BoujeeEnjinia1701/slopewatch/cad/drawings/SLW-DWG-001.pdf

CONCEPT, NOT FOR FABRICATION | SlopeWatch · github.com/BoujeeEnjinia1701/slopewatch

FRONT VIEW
Scale 1:50; looking at the front (along +Y)

TOP VIEW
Scale 1:50; looking down (along -Z)

RIGHT VIEW
Scale 1:50; looking at the right side (along -X)

4628

435 4660

GROUND

3,510 top of beacon

3,200 mast

1,750 node

600

800 embed

400 capsule

1,300 | 1,600

1-3 TILT STAKE (DETAIL A)

4 CRACK GAUGE

6 FIELDNODE CORE

7 ALERT UNIT, SIDE MOUNTED

7 KEYED SWITCH POST

8 MAST (SITE OPTION)

+X DOWNSLOPE ON SITE; NODE AND HORN FACE -Y

DETAIL A
Stake section, scale 1:10

2 CAPSULE 34 x 130

FOAM PLUG

STAND TUBE 40

GROUT 110 x 450

1 PIPE 48.3 x 3.2

3 HEAD 110, CONDUIT IN AND OUT

330

GROUND

MAIN DIMENSIONS AND INTERFACES (MM)
Stake 48.3 x 3.2 galv. pipe, 1000 long, 800 in ground, screwed end cap Hole 110 dia x 829; grout 3.7 L; capsule 400 deep on stand tube Crack gauge: anchors 900 apart, pins 20 x 700, stroke 100
Mast (option) 48.3 x 3.2, 3,200 high; footing 320 x 600
Switch post 26.9 dia, 1,400 high, 5 m from mast on site
FieldNode massing per FND-DDR-003; node bottom 1,750; alert unit on V-blocks and bands Bus 4-core 0.5 mm2 on the 5 V port; stakes 10 m apart, cable 59 m on site
REV | DESCRIPTION | DATE | BY
P1 | Preliminary GA for TRL 3 (from cad/src/model.py) | 2026-09-25 | AC
P2 | Keyed switch on own post 5 m from mast; mast a site option (DDR-002) | 2026-09-25 | AC
P3 | Layout and labels tidied | 2026-09-25 | AC
P4 | Constructable design (DDR-003) | 2026-10-01 | AC
P5 | SLW-DEC-001: stake head marking, back plate wall holes | 2026-10-02 | AC
SLOPEWATCH | github.com/BoujeeEnjinia1701/slopewatch

## General arrangement

DRAWING NO.
SLW-DWG-001

REV
P5

SHEET
1 of 1

SIZE

## ANSI B

SCALE
1:50

UNITS
mm
PROJECTION | DATE
2026-10-02

DRAWN
Amish Chadha

MATERIAL / NOTES
Galvanized steel, cement grout, bought-in parts per bom/bom.csv. PRELIMINARY, NOT FOR FABRICATION
Licensed CERN-OHL-S-2.0 · Design Molecule Lab · designmolecule.com | Generated from cad/src; do not edit by hand
