BoujeeEnjinia1701/slopewatch/cad/drawings/SLW-DWG-101.pdf

BUILD PLAN SKETCH, PLAN NOT YET BUILT SlopeWatch · github.com/BoujeeEnjinia1701/slopewatch

FRONT VIEW
Scale 1:10; looking at the front (along +Y)

TOP VIEW
Scale 1:10; looking down (along -Z)

RIGHT VIEW
Scale 1:10; looking at the right side (along -X)

60

60 1009

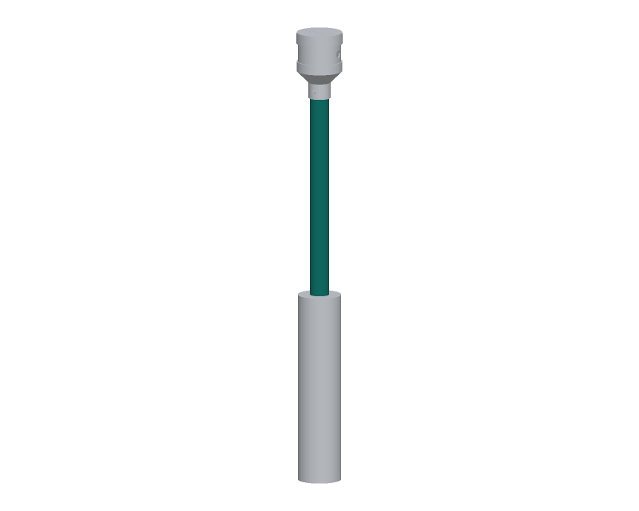
[picture p7: figure]

WHERE IT GOES
This part in colour, its neighbours in grey

HOW TO MAKE IT AND HOW IT FITS
Make three. Cut 1,000 mm of 48.3 x 3.2 mm galvanized pipe with one end threaded 1.5 in (have the merchant cut and thread it). Screw the 1.5 in malleable-iron end cap onto the threaded end with thread sealant, hand tight plus a quarter turn with a pipe wrench. File the other (top) end square and deburr inside and out.
Paint a ground mark round the pipe 200 mm below the top; the pipe goes into the ground up to this mark (800 mm buried).
Touch up cut galvanizing with zinc-rich paint.
Do not drill the head screw holes yet: they are drilled through
the head's socket at assembly so they line up (step 6).
Fit: the cap keeps grout and water out of the bottom; the stand tube stands on the cap's floor inside the pipe.
Check: blow down the pipe; no light or air through the cap.
REV | DESCRIPTION | DATE | BY
P1 | Making sketch for the prototype build plan | 2026-10-01 | AC
SLOPEWATCH | github.com/BoujeeEnjinia1701/slopewatch

## SlopeWatch stake pipe with end cap (make 3): making sketch

DRAWING NO.
SLW-DWG-101

REV
P1

SHEET
1 of 1

SIZE

## ANSI B

SCALE
1:10

UNITS
mm
PROJECTION | DATE
2026-10-01

DRAWN
Amish Chadha

MATERIAL / NOTES
Galvanized steel pipe 48.3 x 3.2 mm (1.5 in), threaded one end; malleable-iron cap
Licensed CERN-OHL-S-2.0 · Design Molecule Lab · designmolecule.com | Generated from cad/src; do not edit by hand
