BoujeeEnjinia1701/slopewatch/cad/drawings/SLW-DWG-102.pdf

BUILD PLAN SKETCH, PLAN NOT YET BUILT SlopeWatch · github.com/BoujeeEnjinia1701/slopewatch

FRONT VIEW
Scale 1:5; looking at the front (along +Y)

TOP VIEW
Scale 1:5; looking down (along -Z)

RIGHT VIEW
Scale 1:5; looking at the right side (along -X)

40

40 335

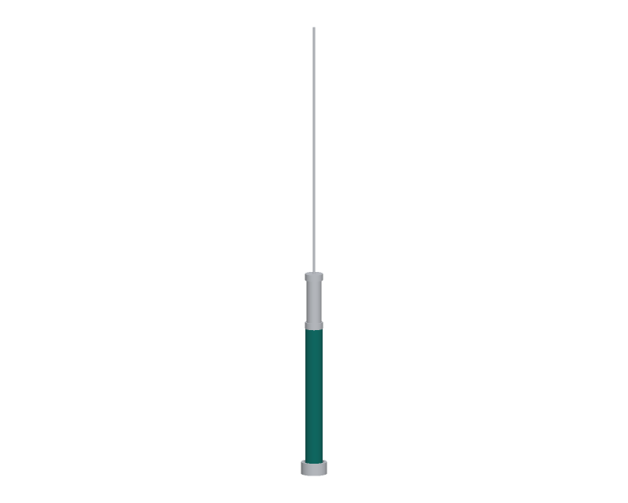
[picture p8: figure]

WHERE IT GOES
This part in colour, its neighbours in grey

HOW TO MAKE IT AND HOW IT FITS
Make three. Cut 335 mm of 40 mm OD PVC pipe, ends square. Deburr both ends; chamfer the outside edges 1 mm so it slides down the 41.9 mm bore of the stake pipe without catching. Its length sets the capsule depth: capsule centre 400 mm below ground when the stand tube sits on the end cap floor. Fit: drops down the pipe and stands on the cap floor, 0.95 mm clear of the bore all round. The capsule's lower collar sits on its top rim; the capsule itself is 1 mm inside the rim.
Mark the length on the tube; check it with a tape before cutting, since a 10 mm error moves the capsule 10 mm.
Check: 335 mm long, within 2 mm; slides freely down an offcut of the stake pipe.
REV | DESCRIPTION | DATE | BY
P1 | Making sketch for the prototype build plan | 2026-10-01 | AC
SLOPEWATCH | github.com/BoujeeEnjinia1701/slopewatch

## SlopeWatch stand tube (make 3): making sketch

DRAWING NO.
SLW-DWG-102

REV
P1

SHEET
1 of 1

SIZE

## ANSI B

SCALE
1:5

UNITS
mm
PROJECTION | DATE
2026-10-01

DRAWN
Amish Chadha

MATERIAL / NOTES
PVC pressure pipe 40 mm OD, 2 mm wall
Licensed CERN-OHL-S-2.0 · Design Molecule Lab · designmolecule.com | Generated from cad/src; do not edit by hand
