BoujeeEnjinia1701/slopewatch/cad/drawings/SLW-DWG-103.pdf

BUILD PLAN SKETCH, PLAN NOT YET BUILT SlopeWatch · github.com/BoujeeEnjinia1701/slopewatch

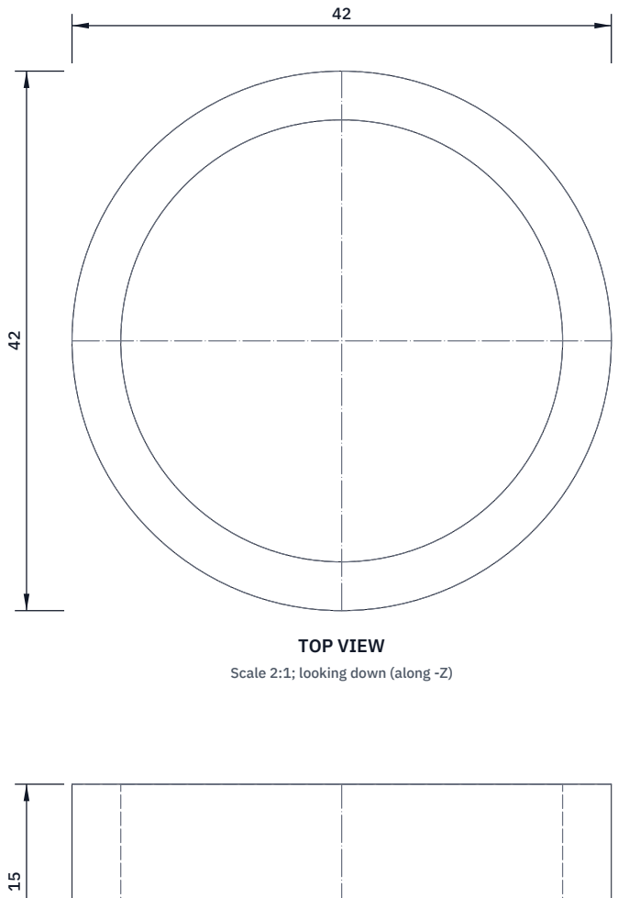
[picture p9: figure]
TOP VIEW; Scale 2:1; looking down (along -Z)

FRONT VIEW
Scale 2:1; looking at the front (along +Y)

RIGHT VIEW
Scale 2:1; looking at the right side (along -X)

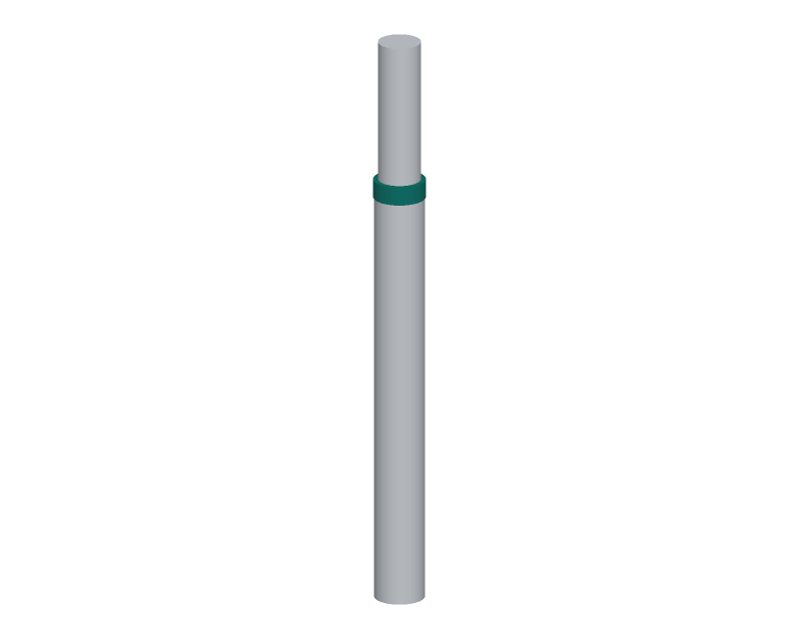
[picture p10: figure]

WHERE IT GOES
This part in colour, its neighbours in grey

HOW TO MAKE IT AND HOW IT FITS
Make six, two per capsule. Print ASA flat, 100 % infill. Ring 41.5 mm outside, 34 mm inside, 15 mm long.
Print one first and check it: it must be a light press fit on
the capsule tube and slide freely in an offcut of the stake
pipe (bore 41.9 mm). Adjust the outside size in steps of 0.2 mm. Fit: one collar flush with each end of the capsule, with a drop
of polyurethane adhesive. They hold the capsule on the pipe axis so it tilts with the pipe; 0.2 mm clearance to the bore.
The lower collar rests on the stand tube's top rim.
Check: on the capsule, both collars turn freely in the pipe offcut and the capsule does not rock when held level.
REV | DESCRIPTION | DATE | BY
P1 | Making sketch for the prototype build plan | 2026-10-01 | AC
SLOPEWATCH | github.com/BoujeeEnjinia1701/slopewatch

## SlopeWatch capsule centring collar (make 6): making sketch

DRAWING NO.
SLW-DWG-103

REV
P1

SHEET
1 of 1

SIZE

## ANSI B

SCALE
2:1

UNITS
mm
PROJECTION | DATE
2026-10-01

DRAWN
Amish Chadha

MATERIAL / NOTES
ASA, 3D printed, 100 % infill
Licensed CERN-OHL-S-2.0 · Design Molecule Lab · designmolecule.com | Generated from cad/src; do not edit by hand
