BoujeeEnjinia1701/slopewatch/cad/drawings/SLW-DWG-104.pdf

BUILD PLAN SKETCH, PLAN NOT YET BUILT SlopeWatch · github.com/BoujeeEnjinia1701/slopewatch

FRONT VIEW
Scale 1:2; looking at the front (along +Y)

TOP VIEW
Scale 1:2; looking down (along -Z)

RIGHT VIEW
Scale 1:2; looking at the right side (along -X)

42

42 130

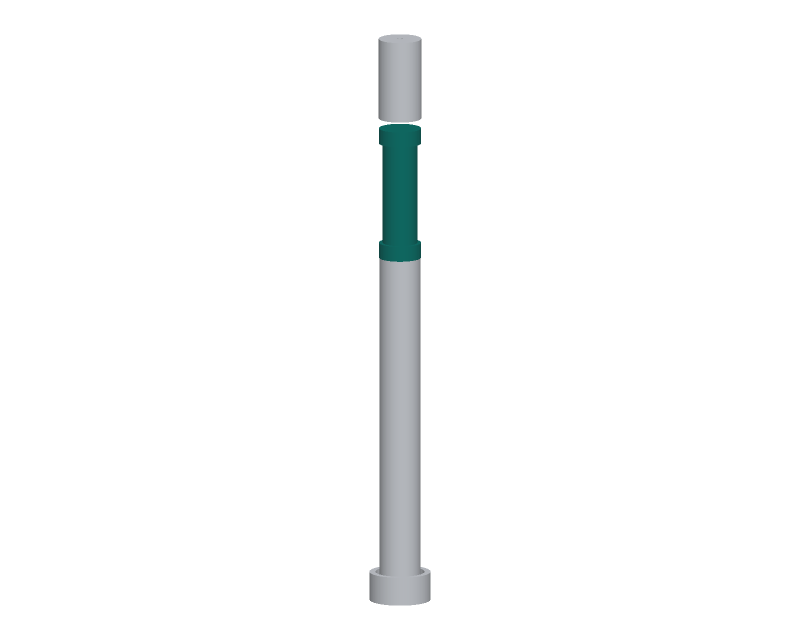
[picture p11: figure]

WHERE IT GOES
This part in colour, its neighbours in grey

HOW TO MAKE IT AND HOW IT FITS
Make three. Tube 34 mm OD x 130 mm, polycarbonate, 2 mm wall. Board: inclinometer, microcontroller, RS-485 transceiver and 3.3 V regulator, at most 28 mm wide, flashed and bench-read first.
Mark the board's X axis with an arrow on the tube label: the arrow points downslope when the capsule is lowered (step 4).
Lead: 0.8 m of 4-core 0.25 mm2 shielded cable, out of the top centre. Seal the bottom with a glued disc, slide the board in on a
printed carrier square to the tube, and pot it full with
polyurethane potting compound; cure as its maker says.
Glue a centring collar flush on each end (SLW-DWG-103). Fit: rests on the stand tube on its lower collar, centred in the pipe by both collars; the foam plug sits 10 mm above it. Check: reads within 0.1 degree of a spirit level on the bench.
REV | DESCRIPTION | DATE | BY
P1 | Making sketch for the prototype build plan | 2026-10-01 | AC
SLOPEWATCH | github.com/BoujeeEnjinia1701/slopewatch

## SlopeWatch sensor capsule (make 3): making sketch

DRAWING NO.
SLW-DWG-104

REV
P1

SHEET
1 of 1

SIZE

## ANSI B

SCALE
1:2

UNITS
mm
PROJECTION | DATE
2026-10-01

DRAWN
Amish Chadha

MATERIAL / NOTES
Polycarbonate tube 34 x 2 mm, potted electronics
Licensed CERN-OHL-S-2.0 · Design Molecule Lab · designmolecule.com | Generated from cad/src; do not edit by hand
