BoujeeEnjinia1701/slopewatch/cad/drawings/SLW-DWG-105.pdf

BUILD PLAN SKETCH, PLAN NOT YET BUILT SlopeWatch · github.com/BoujeeEnjinia1701/slopewatch

FRONT VIEW
Scale 1:5; looking at the front (along +Y)

TOP VIEW
Scale 1:5; looking down (along -Z)

RIGHT VIEW
Scale 1:5; looking at the right side (along -X)

176

117 170

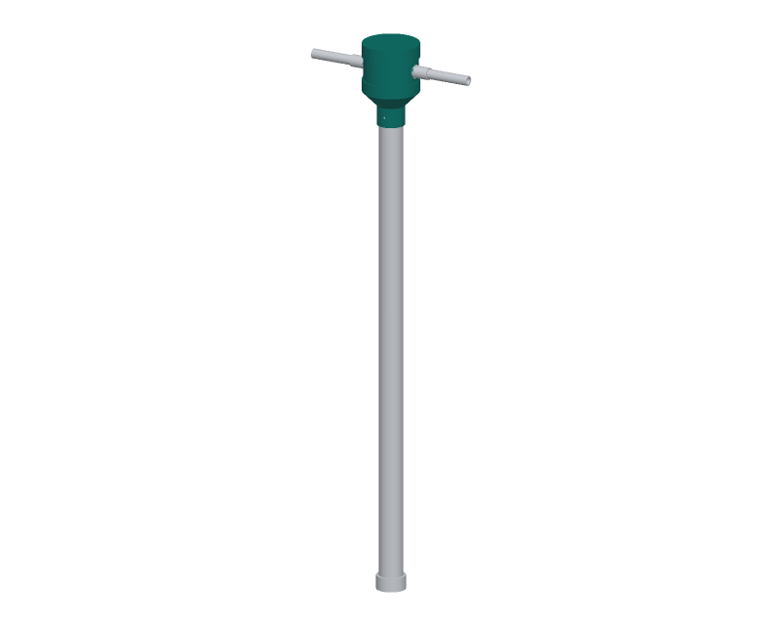
[picture p12: figure]

WHERE IT GOES
This part in colour, its neighbours in grey

HOW TO MAKE IT AND HOW IT FITS
Make three from stock 110 mm PVC drainage parts: a 110 x 50 mm concentric reducer, a 110 mm end cap and 94 mm of 110 mm pipe. Cut the 110 pipe square to 94 mm and deburr.
Drill two 20.5 mm holes for the M20 conduit fittings, opposite each other, centred 46 mm up from the pipe's lower end (check the fitting's datasheet). One faces upslope, one downslope.
Push the pipe fully into the reducer's 110 socket and the cap onto its top; solvent-cement both joints.
Paint the outside signal amber. Round the cap skirt wind 25 mm retroreflective tape; stick a 40 x 30 mm ID label on the -Y side and an arrow on the crown pointing downslope (+X).
Fit: the reducer's 50 mm socket goes over the stake pipe on a tape wrap; two M5 self-tapping screws hold it, drilled through the socket into the pipe at assembly, 20 mm above the socket rim. Check: the head stands 330 mm above ground on the stake.
REV | DESCRIPTION | DATE | BY
P1 | Making sketch for the prototype build plan | 2026-10-01 | AC
P2 | SLW-DEC-001: head marking, wall holes, 60.3 mm site mast | 2026-10-02 | AC
SLOPEWATCH | github.com/BoujeeEnjinia1701/slopewatch

## SlopeWatch stake head (make 3): making sketch

DRAWING NO.
SLW-DWG-105

REV
P2

SHEET
1 of 1

SIZE

## ANSI B

SCALE
1:5

UNITS
mm
PROJECTION | DATE
2026-10-02

DRAWN
Amish Chadha

MATERIAL / NOTES
Stock PVC drainage fittings, 110 mm
Licensed CERN-OHL-S-2.0 · Design Molecule Lab · designmolecule.com | Generated from cad/src; do not edit by hand
