BoujeeEnjinia1701/slopewatch/cad/drawings/SLW-DWG-106.pdf

BUILD PLAN SKETCH, PLAN NOT YET BUILT SlopeWatch · github.com/BoujeeEnjinia1701/slopewatch

FRONT VIEW
Scale 1:10; looking at the front (along +Y)

TOP VIEW
Scale 1:10; looking down (along -Z)

RIGHT VIEW
Scale 1:10; looking at the right side (along -X)

20

20 700

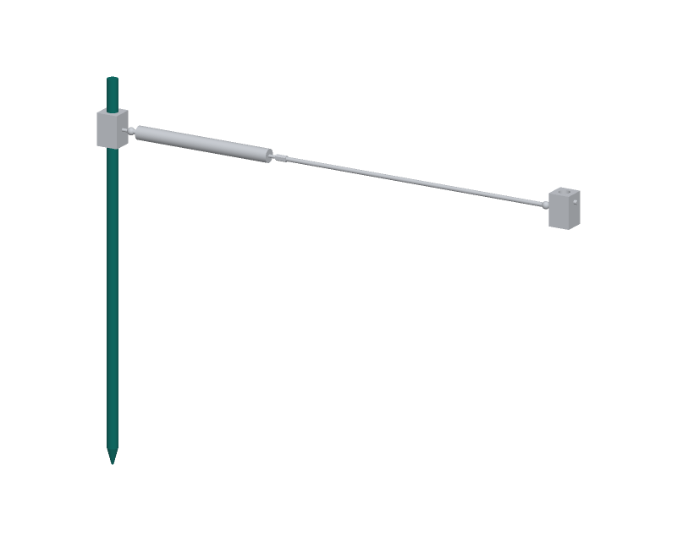
[picture p13: figure]

WHERE IT GOES
This part in colour, its neighbours in grey

HOW TO MAKE IT AND HOW IT FITS
Make two. Cut 700 mm of 20 mm round bar.
Grind a point 30 mm long on one end, about 4 mm across the tip. Chamfer the top edge 2 mm so a sledge does not mushroom it. Paint a ring 500 mm from the tip: drive to this ring, which leaves 200 mm above ground.
Paint the exposed part (or use galvanized bar).
Fit: driven upright 900 mm apart, one each side of the crack, on a line square to it. Each carries a clamp block with its centre 110 mm above ground.
Check: a level on the pin shows it upright within 2 degrees.
REV | DESCRIPTION | DATE | BY
P1 | Making sketch for the prototype build plan | 2026-10-01 | AC
SLOPEWATCH | github.com/BoujeeEnjinia1701/slopewatch

## SlopeWatch anchor pin (make 2): making sketch

DRAWING NO.
SLW-DWG-106

REV
P1

SHEET
1 of 1

SIZE

## ANSI B

SCALE
1:10

UNITS
mm
PROJECTION | DATE
2026-10-01

DRAWN
Amish Chadha

MATERIAL / NOTES
Mild steel round bar 20 mm, galvanized or painted
Licensed CERN-OHL-S-2.0 · Design Molecule Lab · designmolecule.com | Generated from cad/src; do not edit by hand
