BoujeeEnjinia1701/slopewatch/cad/drawings/SLW-DWG-107.pdf

BUILD PLAN SKETCH, PLAN NOT YET BUILT SlopeWatch · github.com/BoujeeEnjinia1701/slopewatch

FRONT VIEW
Scale 1:1; looking at the front (along +Y)

TOP VIEW
Scale 1:1; looking down (along -Z)

RIGHT VIEW
Scale 1:1; looking at the right side (along -X)

40

40 60

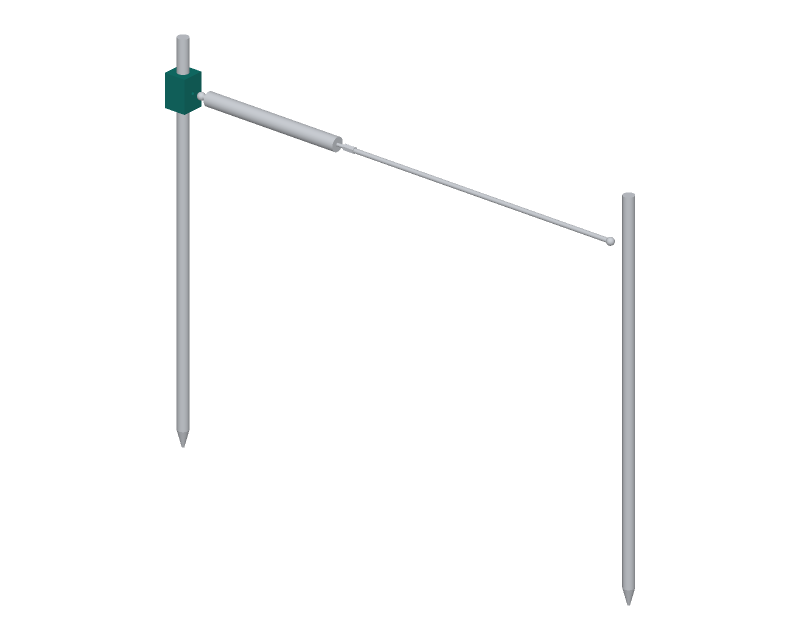
[picture p14: figure]

WHERE IT GOES
This part in colour, its neighbours in grey

HOW TO MAKE IT AND HOW IT FITS
Make two the same. Saw 60 mm off 40 x 40 mm bar; file square. Bore: drill 20.5 mm right through the 40 x 40 faces, on centre. Stud hole: on one 40 x 60 side face, at mid-height (30 mm up) and centred, drill 5.0 mm 12 deep and tap M6 10 deep.
Set screw hole: on the opposite side face, 45 mm up and centred, drill 6.8 mm through into the bore and tap M8.
Fit: slides onto the pin; the stud face points at the other pin across the crack. Set the block centre 110 mm above ground and tighten the M8 set screw onto the pin.
Screw the M6 stud of a rod-end ball joint 10 mm into the stud hole with medium threadlocker.
Check: the block slides on a 20 mm bar with no shake beyond 0.5 mm.
REV | DESCRIPTION | DATE | BY
P1 | Making sketch for the prototype build plan | 2026-10-01 | AC
SLOPEWATCH | github.com/BoujeeEnjinia1701/slopewatch

## SlopeWatch crack gauge clamp block (make 2): making sketch

DRAWING NO.
SLW-DWG-107

REV
P1

SHEET
1 of 1

SIZE

## ANSI B

SCALE
1:1

UNITS
mm
PROJECTION | DATE
2026-10-01

DRAWN
Amish Chadha

MATERIAL / NOTES
Aluminium square bar 40 x 40 mm, 6082
Licensed CERN-OHL-S-2.0 · Design Molecule Lab · designmolecule.com | Generated from cad/src; do not edit by hand
