BoujeeEnjinia1701/slopewatch/cad/drawings/SLW-DWG-108.pdf

BUILD PLAN SKETCH, PLAN NOT YET BUILT SlopeWatch · github.com/BoujeeEnjinia1701/slopewatch

FRONT VIEW
Scale 1:5; looking at the front (along +Y)

TOP VIEW
Scale 1:5; looking down (along -Z)

RIGHT VIEW
Scale 1:5; looking at the right side (along -X)

8

8 501

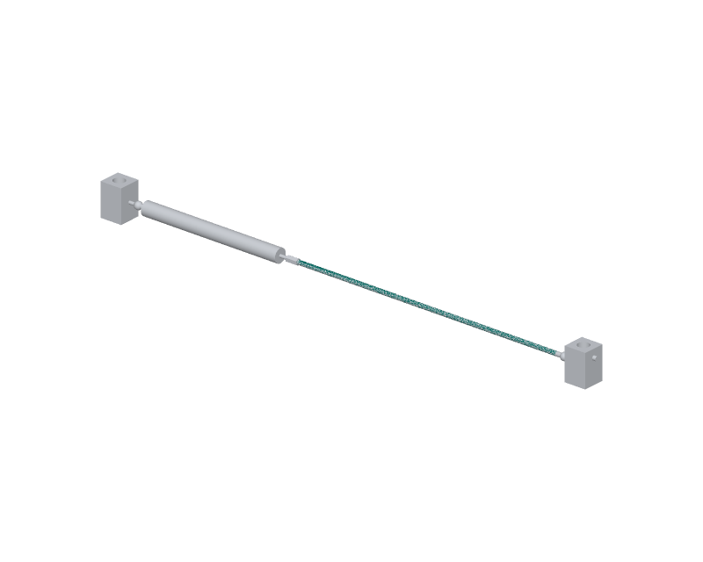
[picture p15: figure]

WHERE IT GOES
This part in colour, its neighbours in grey

HOW TO MAKE IT AND HOW IT FITS
Cut 501 mm of 8 mm stainless bar, ends square.
Centre-drill each end in a drill press with the bar held
upright in a V-block; drill 5.0 mm 15 deep and tap M6.
Screw an M6 x 20 stud into each end with medium threadlocker, 10 mm in and 10 mm out.
Fit: one end into the coupling nut on the sensor's plunger; the other into the downslope rod-end ball joint on its stud.
Set the plunger 15 mm out of the sensor body before tightening, so the gauge can read 85 mm of opening and 15 mm of closing. Check: 501 mm long within 1 mm; straight within 1 mm
when rolled on a flat bench.
REV | DESCRIPTION | DATE | BY
P1 | Making sketch for the prototype build plan | 2026-10-01 | AC
SLOPEWATCH | github.com/BoujeeEnjinia1701/slopewatch

## SlopeWatch crack gauge extension rod: making sketch

DRAWING NO.
SLW-DWG-108

REV
P1

SHEET
1 of 1

SIZE

## ANSI B

SCALE
1:5

UNITS
mm
PROJECTION | DATE
2026-10-01

DRAWN
Amish Chadha

MATERIAL / NOTES
Stainless steel round bar 8 mm, 304
Licensed CERN-OHL-S-2.0 · Design Molecule Lab · designmolecule.com | Generated from cad/src; do not edit by hand
