BoujeeEnjinia1701/slopewatch/cad/drawings/SLW-DWG-109.pdf

BUILD PLAN SKETCH, PLAN NOT YET BUILT SlopeWatch · github.com/BoujeeEnjinia1701/slopewatch

FRONT VIEW
Scale 1:10; looking at the front (along +Y)

TOP VIEW
Scale 1:10; looking down (along -Z)

RIGHT VIEW
Scale 1:10; looking at the right side (along -X)

1150

250 250

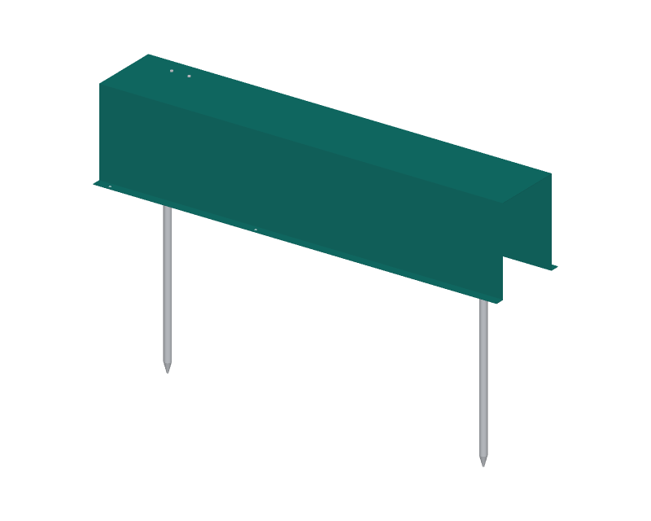
[picture p16: figure]

WHERE IT GOES
This part in colour, its neighbours in grey

HOW TO MAKE IT AND HOW IT FITS
Blank 1,150 x 750 mm of 1.5 mm galvanized sheet. Fold lines along the 1,150 mm length at 25, 275, 475 and 725 mm from one edge. Fold the two outer 25 mm strips out (feet) and the 250 mm legs down, to an inverted channel 200 wide, 250 high, with feet.
Have it folded by a sheet metal shop, or fold it between two
1.2 m steel angles clamped to a bench.
Peg holes: four 9 mm, centred in the feet, 40 and 455 mm from the upslope end. Only the upslope half is pegged, so the crack
can open under the downslope half.
Reader screw holes: two 4.5 mm in the web, 100 and 150 mm from the upslope end, 52 mm to one side of the centre line.
Fit: stands over the gauge on its feet, 48 mm above the pin tops. Check: the web is flat and the legs square within 3 mm.
REV | DESCRIPTION | DATE | BY
P1 | Making sketch for the prototype build plan | 2026-10-01 | AC
SLOPEWATCH | github.com/BoujeeEnjinia1701/slopewatch

## SlopeWatch crack gauge guard: making sketch

DRAWING NO.
SLW-DWG-109

REV
P1

SHEET
1 of 1

SIZE

## ANSI B

SCALE
1:10

UNITS
mm
PROJECTION | DATE
2026-10-01

DRAWN
Amish Chadha

MATERIAL / NOTES
Galvanized steel sheet 1.5 mm
Licensed CERN-OHL-S-2.0 · Design Molecule Lab · designmolecule.com | Generated from cad/src; do not edit by hand
