BoujeeEnjinia1701/slopewatch/cad/drawings/SLW-DWG-110.pdf

BUILD PLAN SKETCH, PLAN NOT YET BUILT SlopeWatch · github.com/BoujeeEnjinia1701/slopewatch

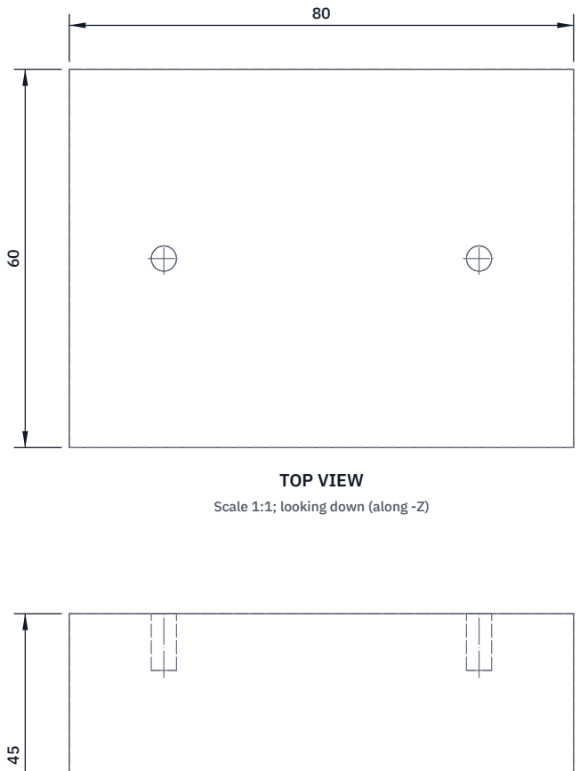
[picture p17: figure]
TOP VIEW; Scale 1:1; looking down (along -Z)

FRONT VIEW
Scale 1:1; looking at the front (along +Y)

RIGHT VIEW
Scale 1:1; looking at the right side (along -X)

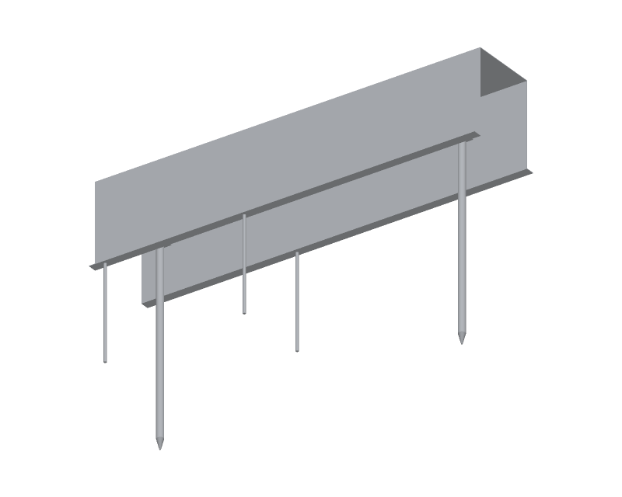
[picture p18: figure]

WHERE IT GOES
This part in colour, its neighbours in grey

HOW TO MAKE IT AND HOW IT FITS
A bought IP67 box, 80 x 60 x 45 mm, holding the reader board. Base (the face that goes against the guard web): two 4 mm holes 50 mm apart on the long centre line, matching the web holes. Seal under each screw head with a nylon washer.
Downslope end: one 20.5 mm hole, centred, for the M20 conduit fitting that carries the bus out.
Upslope end: one 12.5 mm hole for an M12 gland for the sensor lead. Fit the reader board on its standoffs; terminate the sensor lead
and the bus in lever connectors as the bus diagram shows.
Fit: hangs under the guard web at the upslope end, lid down,
12 mm clear of the upslope pin.
Check: lid gasket seated; the box hangs level.
REV | DESCRIPTION | DATE | BY
P1 | Making sketch for the prototype build plan | 2026-10-01 | AC
SLOPEWATCH | github.com/BoujeeEnjinia1701/slopewatch

## SlopeWatch crack gauge reader box: drilling sketch

DRAWING NO.
SLW-DWG-110

REV
P1

SHEET
1 of 1

SIZE

## ANSI B

SCALE
1:1

UNITS
mm
PROJECTION | DATE
2026-10-01

DRAWN
Amish Chadha

MATERIAL / NOTES
Bought IP67 box 80 x 60 x 45 mm
Licensed CERN-OHL-S-2.0 · Design Molecule Lab · designmolecule.com | Generated from cad/src; do not edit by hand
