BoujeeEnjinia1701/slopewatch/cad/drawings/SLW-DWG-111.pdf

BUILD PLAN SKETCH, PLAN NOT YET BUILT SlopeWatch · github.com/BoujeeEnjinia1701/slopewatch

FRONT VIEW
Scale 1:5; looking at the front (along +Y)

TOP VIEW
Scale 1:5; looking down (along -Z)

RIGHT VIEW
Scale 1:5; looking at the right side (along -X)

160

3 360

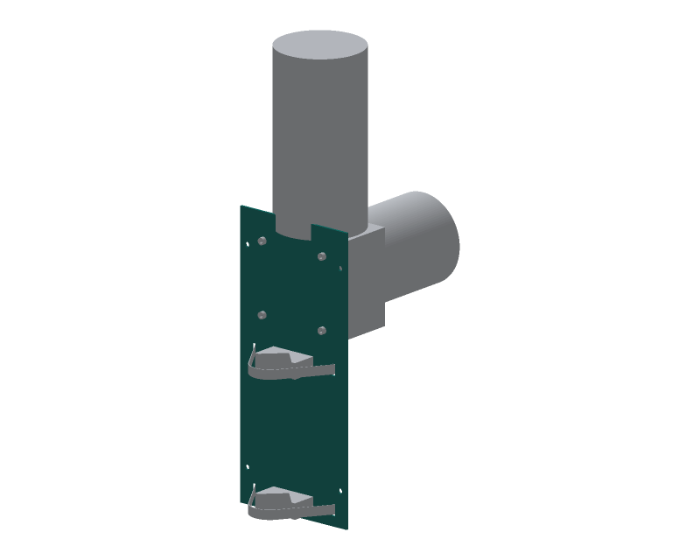
[picture p19: figure]

WHERE IT GOES
This part in colour, its neighbours in grey

HOW TO MAKE IT AND HOW IT FITS
Blank 160 x 360 mm of 3 mm aluminium; round corners 2 mm. Heights from the bottom edge; sideways from the centre line. Band slots 6 x 15 mm at 60 mm each side, centred 20 and
190 mm up: chain drill 3 mm, file square.
V-block screws: 4.5 mm at 18 mm each side, 20 and 190 mm up, countersunk from the front.
Alert box screws: 5.5 mm at 45 mm each side, 235 and 325 mm up. Wall holes: four 6.5 mm at 70 mm each side, 45 and 315 mm up, for M6 coach screws into a timber pole or wall.
Deburr every hole and edge.
Fit: V-blocks on the back; the alert box on the front, top part;
the two band clamps go round the pole through the slots below the box. The top 110 mm stands above a mast top.
Check: lay the V-blocks and box on it and look through each hole.
REV | DESCRIPTION | DATE | BY
P1 | Making sketch for the prototype build plan | 2026-10-01 | AC
P2 | SLW-DEC-001: head marking, wall holes, 60.3 mm site mast | 2026-10-02 | AC
SLOPEWATCH | github.com/BoujeeEnjinia1701/slopewatch

## SlopeWatch alert unit back plate: making sketch

DRAWING NO.
SLW-DWG-111

REV
P2

SHEET
1 of 1

SIZE

## ANSI B

SCALE
1:5

UNITS
mm
PROJECTION | DATE
2026-10-02

DRAWN
Amish Chadha

MATERIAL / NOTES
Aluminium sheet 3 mm, 5052 or 6061
Licensed CERN-OHL-S-2.0 · Design Molecule Lab · designmolecule.com | Generated from cad/src; do not edit by hand
