BoujeeEnjinia1701/slopewatch/cad/drawings/SLW-DWG-112.pdf

BUILD PLAN SKETCH, PLAN NOT YET BUILT SlopeWatch · github.com/BoujeeEnjinia1701/slopewatch

FRONT VIEW
Scale 2:1; looking at the front (along +Y)

TOP VIEW
Scale 2:1; looking down (along -Z)

RIGHT VIEW
Scale 2:1; looking at the right side (along -X)

60

33 20

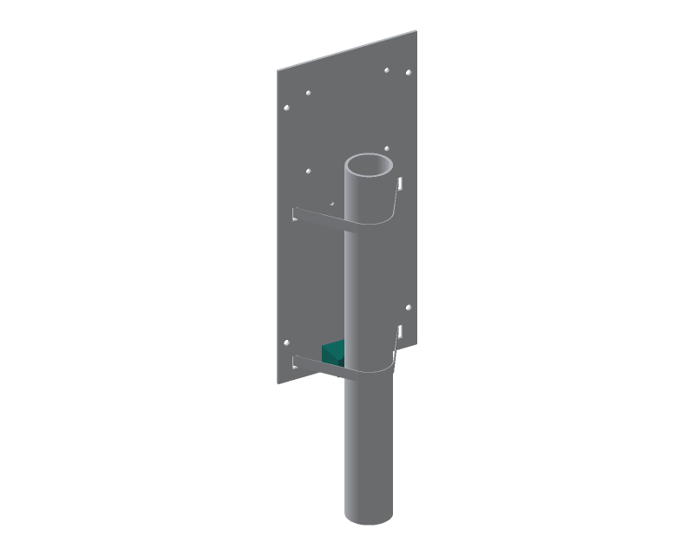
[picture p20: figure]

WHERE IT GOES
This part in colour, its neighbours in grey

HOW TO MAKE IT AND HOW IT FITS
Make two, the same as the FieldNode V-block (FND-DWG-102). Saw a 20 mm slice off 60 x 40 mm bar; saw and file it to
60 wide x 33 deep x 20 tall. The flat back goes on the plate.
Scribe a 90 degree V on both 60 x 33 faces with a 45 degree square: 50.3 mm wide at the front face, point 7.8 mm from the back face. Saw inside both lines and file to them; keep the V faces flat.
Break the V's front edges 0.5 mm.
Drill 3.3 mm 14 deep and tap M4 12 deep in the back face, 18 mm each side of centre, half way up.
Fit: two M4 countersunk screws from the front of the plate. A 48.3 mm pole touches both V faces; 40 to 70 mm poles also seat. Check: on a 48 mm tube it must not rock.
REV | DESCRIPTION | DATE | BY
P1 | Making sketch for the prototype build plan | 2026-10-01 | AC
SLOPEWATCH | github.com/BoujeeEnjinia1701/slopewatch

## SlopeWatch alert unit V-block (make 2): making sketch

DRAWING NO.
SLW-DWG-112

REV
P1

SHEET
1 of 1

SIZE

## ANSI B

SCALE
2:1

UNITS
mm
PROJECTION | DATE
2026-10-01

DRAWN
Amish Chadha

MATERIAL / NOTES
Aluminium flat bar 60 x 40 mm, 6082 or 6061
Licensed CERN-OHL-S-2.0 · Design Molecule Lab · designmolecule.com | Generated from cad/src; do not edit by hand
