BoujeeEnjinia1701/slopewatch/cad/drawings/SLW-DWG-113.pdf

BUILD PLAN SKETCH, PLAN NOT YET BUILT SlopeWatch · github.com/BoujeeEnjinia1701/slopewatch

FRONT VIEW
Scale 1:2; looking at the front (along +Y)

TOP VIEW
Scale 1:2; looking down (along -Z)

RIGHT VIEW
Scale 1:2; looking at the right side (along -X)

120

90 120

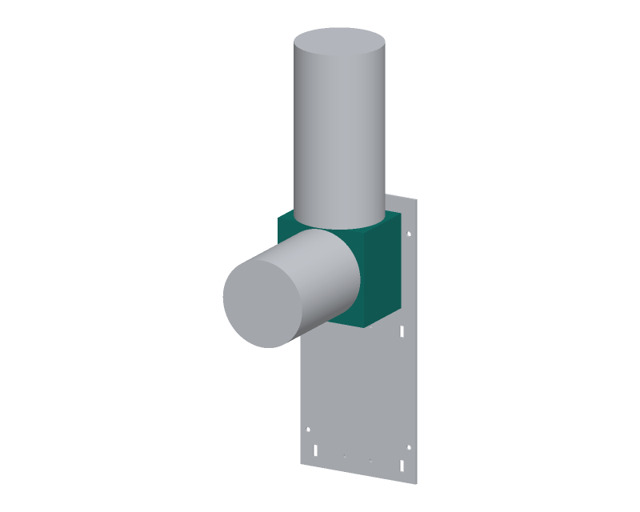
[picture p21: figure]

WHERE IT GOES
This part in colour, its neighbours in grey

HOW TO MAKE IT AND HOW IT FITS
A bought IP65 box, 120 wide x 90 deep x 120 tall, with four corner screw holes outside the lid seal (90 x 90 mm apart).
Bottom: two 16.2 mm holes 30 mm each side of centre, for M16 glands: the lead to the node and the switch lead.
Top: one 10 mm hole, centred, for the beacon lead; the beacon base covers it with its own gasket and three screws.
Front (lid side faces forward): one 10 mm hole, centred, for the horn leads; the horn's flange and gasket cover it.
Tape the faces, pilot drill 3 mm slowly, open with a step drill. Fit the MOSFET driver inside on its standoffs.
Fit: four M5 screws through the corner holes and the back plate, nyloc nuts behind the plate.
Check: every hole covered by a gland, gasket or flange.
REV | DESCRIPTION | DATE | BY
P1 | Making sketch for the prototype build plan | 2026-10-01 | AC
SLOPEWATCH | github.com/BoujeeEnjinia1701/slopewatch

## SlopeWatch alert box: drilling sketch

DRAWING NO.
SLW-DWG-113

REV
P1

SHEET
1 of 1

SIZE

## ANSI B

SCALE
1:2

UNITS
mm
PROJECTION | DATE
2026-10-01

DRAWN
Amish Chadha

MATERIAL / NOTES
Bought IP65 box 120 x 90 x 120 mm, corner holes outside the seal
Licensed CERN-OHL-S-2.0 · Design Molecule Lab · designmolecule.com | Generated from cad/src; do not edit by hand
