BoujeeEnjinia1701/slopewatch/cad/drawings/SLW-DWG-114.pdf

BUILD PLAN SKETCH, PLAN NOT YET BUILT SlopeWatch · github.com/BoujeeEnjinia1701/slopewatch

FRONT VIEW
Scale 1:20; looking at the front (along +Y)

TOP VIEW
Scale 1:20; looking down (along -Z)

RIGHT VIEW
Scale 1:20; looking at the right side (along -X)

27

27 1900

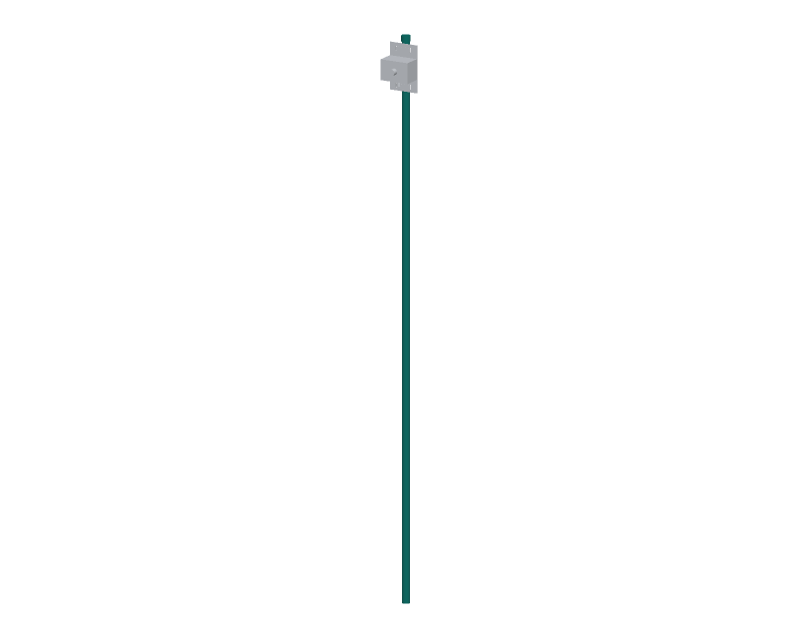
[picture p22: figure]

WHERE IT GOES
This part in colour, its neighbours in grey

HOW TO MAKE IT AND HOW IT FITS
Cut 1,900 mm of 26.9 x 2.6 mm galvanized tube.
Cut the lower end at 45 degrees so it drives more easily; file the top end square and deburr.
Paint a ground mark 500 mm from the lower tip.
Touch up cut ends with zinc-rich paint.
Push a 27 mm plastic tube cap onto the top end.
Fit: driven upright 500 mm into the ground with a post
driver, about 5 m from the mast on the side away from the horn.
The switch back plate clamps to it with two hose clips, the switch
box centre 1,300 mm above ground.
Check: upright within 2 degrees; does not move when pushed by hand.
REV | DESCRIPTION | DATE | BY
P1 | Making sketch for the prototype build plan | 2026-10-01 | AC
SLOPEWATCH | github.com/BoujeeEnjinia1701/slopewatch

## SlopeWatch keyed switch post: making sketch

DRAWING NO.
SLW-DWG-114

REV
P1

SHEET
1 of 1

SIZE

## ANSI B

SCALE
1:20

UNITS
mm
PROJECTION | DATE
2026-10-01

DRAWN
Amish Chadha

MATERIAL / NOTES
Galvanized steel tube 26.9 x 2.6 mm (3/4 in)
Licensed CERN-OHL-S-2.0 · Design Molecule Lab · designmolecule.com | Generated from cad/src; do not edit by hand
