BoujeeEnjinia1701/slopewatch/cad/drawings/SLW-DWG-115.pdf

BUILD PLAN SKETCH, PLAN NOT YET BUILT SlopeWatch · github.com/BoujeeEnjinia1701/slopewatch

FRONT VIEW
Scale 1:2; looking at the front (along +Y)

TOP VIEW
Scale 1:2; looking down (along -Z)

RIGHT VIEW
Scale 1:2; looking at the right side (along -X)

100

3 160

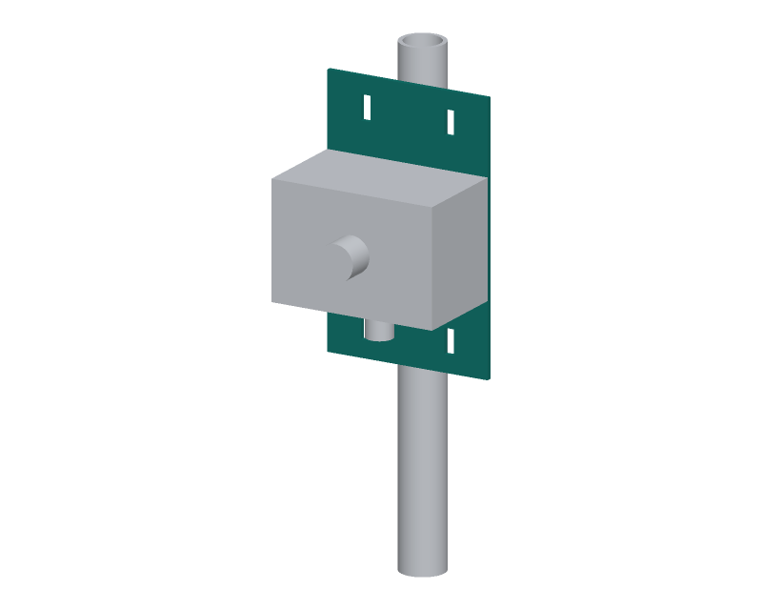
[picture p23: figure]

WHERE IT GOES
This part in colour, its neighbours in grey

HOW TO MAKE IT AND HOW IT FITS
Blank 100 x 160 mm of 3 mm galvanized sheet; round corners. Heights from the bottom edge; sideways from the centre line. Hose clip slots 6 x 15 mm at 26 mm each side, centred 18
and 142 mm up: chain drill 3 mm, file square.
Box screw holes: four 4.5 mm at 40 mm each side, 52 and 108 mm up (match them to your box's corner holes).
Deburr and touch up with zinc-rich paint.
Fit: the back of the plate bears on the post; two 20 to 32 mm stainless hose clips go round the post, through the slots and across the plate front, above and below the box.
Check: the plate does not turn on the post when the clips are tight.
REV | DESCRIPTION | DATE | BY
P1 | Making sketch for the prototype build plan | 2026-10-01 | AC
SLOPEWATCH | github.com/BoujeeEnjinia1701/slopewatch

## SlopeWatch keyed switch back plate: making sketch

DRAWING NO.
SLW-DWG-115

REV
P1

SHEET
1 of 1

SIZE

## ANSI B

SCALE
1:2

UNITS
mm
PROJECTION | DATE
2026-10-01

DRAWN
Amish Chadha

MATERIAL / NOTES
Galvanized steel sheet 3 mm
Licensed CERN-OHL-S-2.0 · Design Molecule Lab · designmolecule.com | Generated from cad/src; do not edit by hand
