BoujeeEnjinia1701/slopewatch/cad/drawings/SLW-DWG-116.pdf

BUILD PLAN SKETCH, PLAN NOT YET BUILT SlopeWatch · github.com/BoujeeEnjinia1701/slopewatch

FRONT VIEW
Scale 1:50; looking at the front (along +Y)

TOP VIEW
Scale 1:50; looking down (along -Z)

RIGHT VIEW
Scale 1:50; looking at the right side (along -X)

48

48 3750

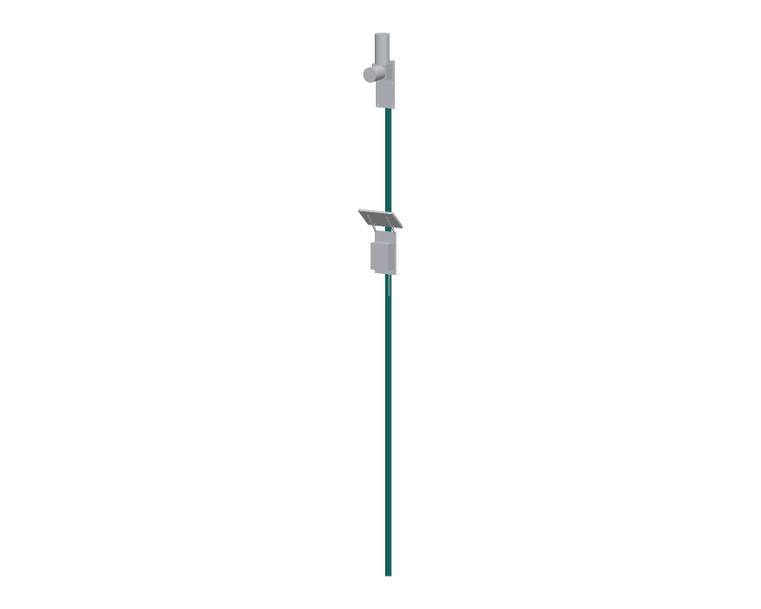
[picture p24: figure]

WHERE IT GOES
This part in colour, its neighbours in grey

HOW TO MAKE IT AND HOW IT FITS
Only where the site has no 40 to 70 mm pole for the node and the alert unit. Prototype mast: 3,750 mm of 48.3 x 3.2 mm galvanized pipe (fenced test slope only); a working site uses 60.3 x 3.6 mm pipe.
File both ends square; touch up with zinc-rich paint.
Paint a ground mark 550 mm from the lower end.
Push a 48 mm plastic pipe cap onto the top end.
Fit: cast 550 mm into a 320 mm x 600 mm concrete footing, plumb. FieldNode bottom 1,750 mm above ground; alert unit back plate 2,950 to 3,310 mm, its top 110 mm above the mast top.
Bonding clamp round the mast 20 to 40 mm above the footing;
16 mm2 bond to the earth rod clamp 450 mm away.
Check: plumb within 1 degree after the concrete has set.
REV | DESCRIPTION | DATE | BY
P1 | Making sketch for the prototype build plan | 2026-10-01 | AC
P2 | SLW-DEC-001: head marking, wall holes, 60.3 mm site mast | 2026-10-02 | AC
SLOPEWATCH | github.com/BoujeeEnjinia1701/slopewatch

## SlopeWatch mast (site option): making sketch

DRAWING NO.
SLW-DWG-116

REV
P2

SHEET
1 of 1

SIZE

## ANSI B

SCALE
1:50

UNITS
mm
PROJECTION | DATE
2026-10-02

DRAWN
Amish Chadha

MATERIAL / NOTES
Galvanized steel pipe 48.3 x 3.2 mm (1.5 in)
Licensed CERN-OHL-S-2.0 · Design Molecule Lab · designmolecule.com | Generated from cad/src; do not edit by hand
