BoujeeEnjinia1701/slopewatch/cad/drawings/SLW-DWG-001.png

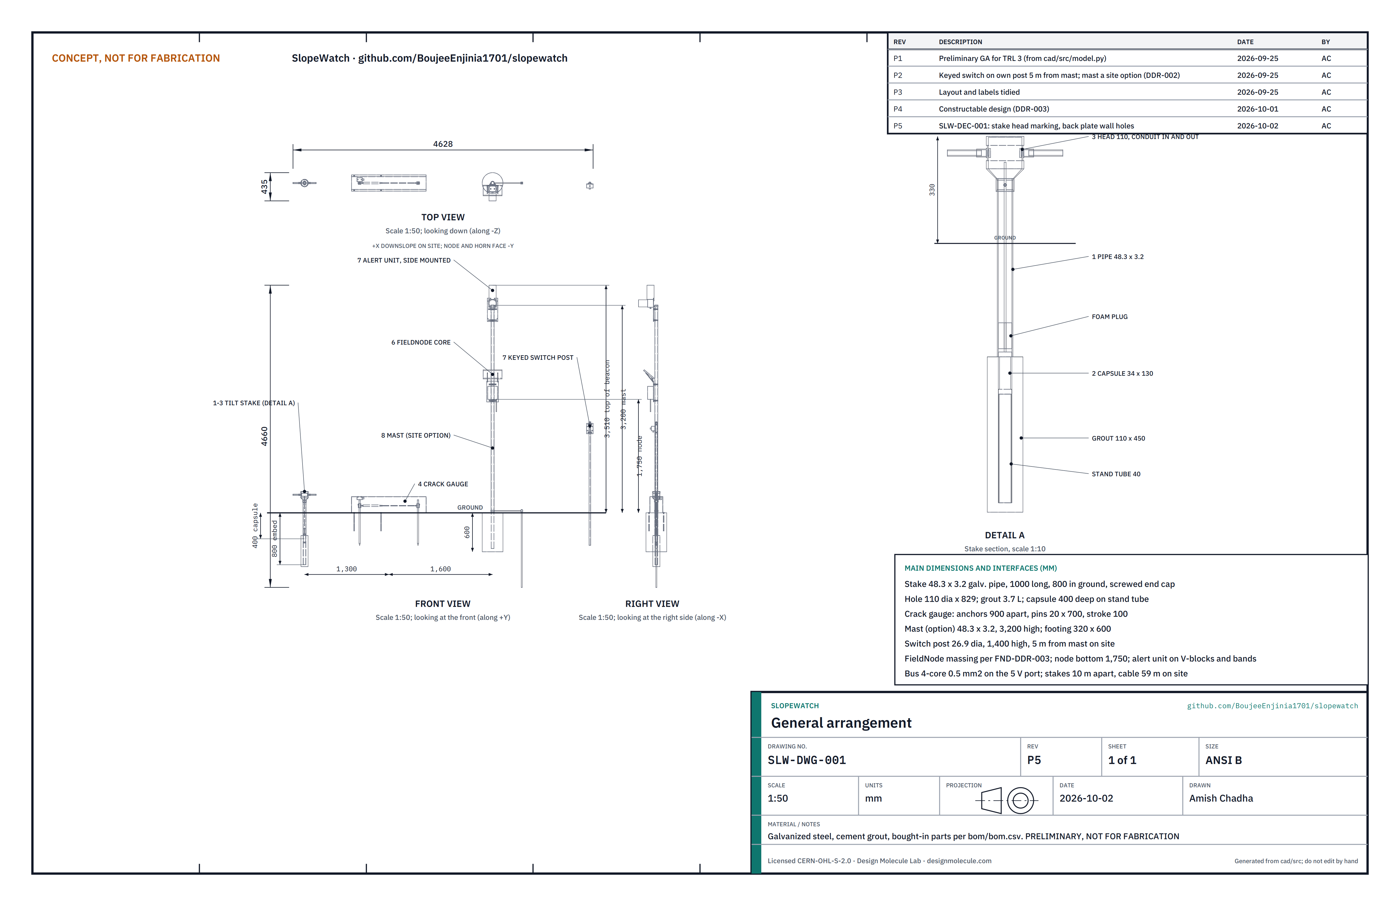
cad/drawings/SLW-DWG-001.png
