BoujeeEnjinia1701/slopewatch/media/card.png

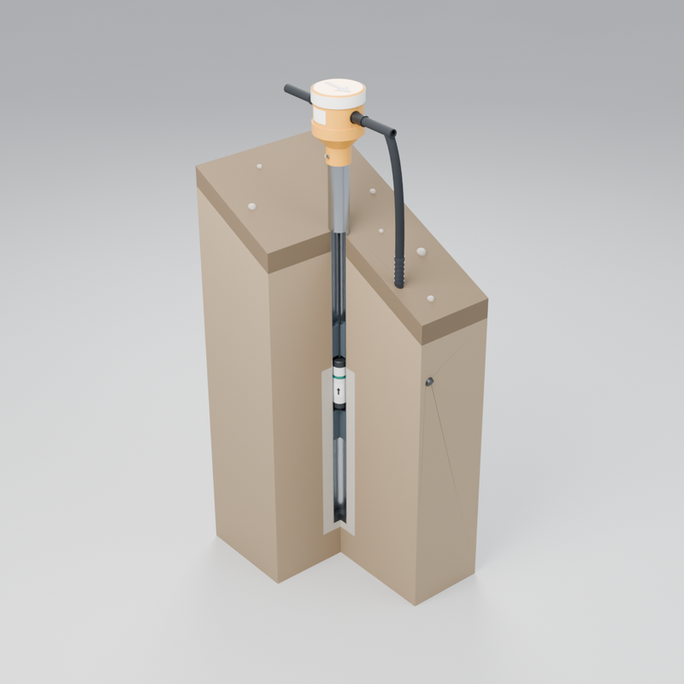
media/card.png
