BoujeeEnjinia1701/slopewatch/media/concept-blueprint.png

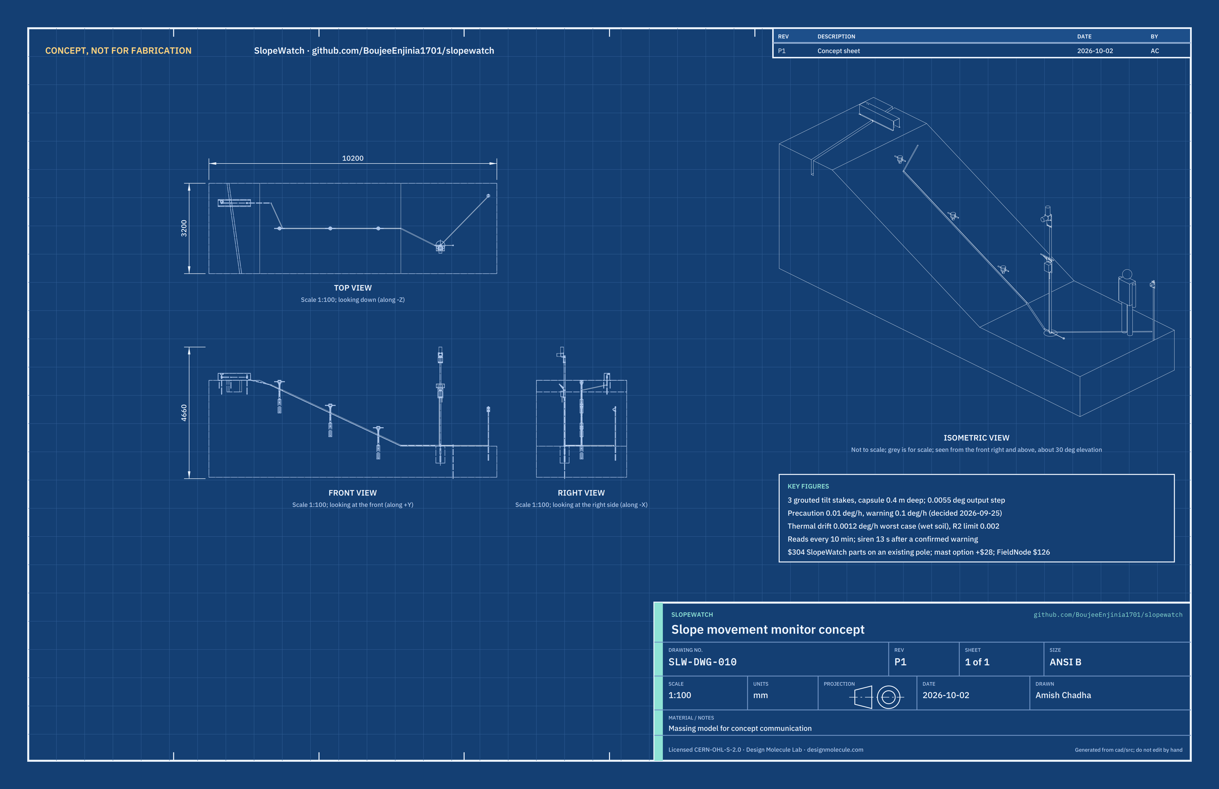
media/concept-blueprint.png
