BoujeeEnjinia1701/slopewatch/media/render-detail.png

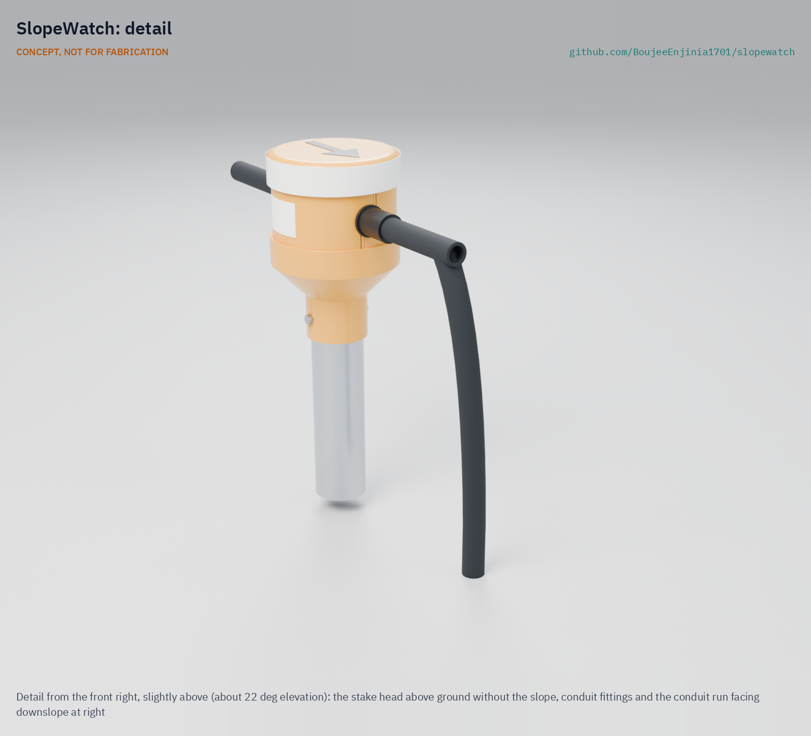
media/render-detail.png
