BoujeeEnjinia1701/slopewatch/media/render-exploded.png

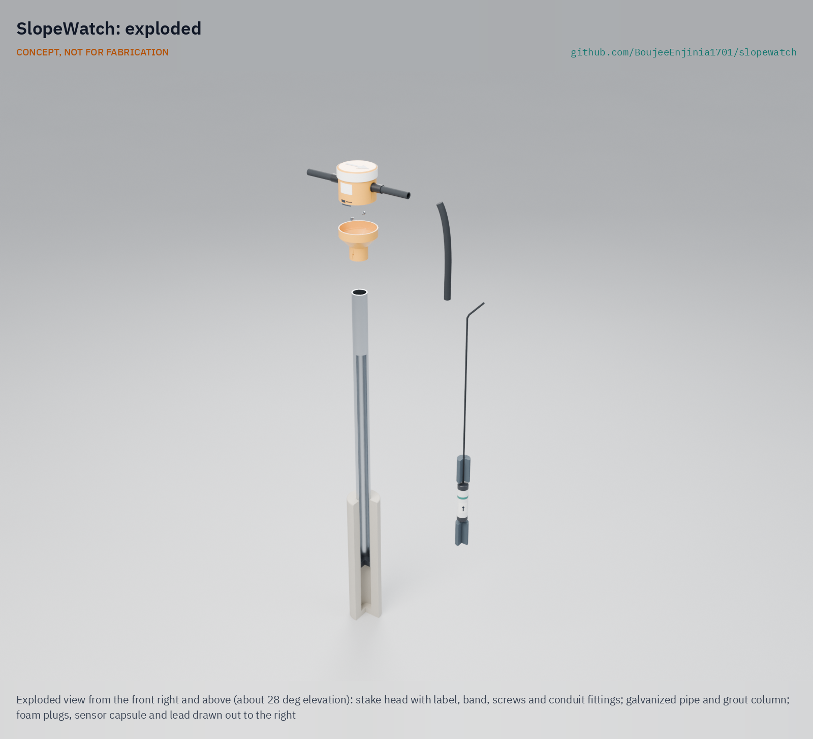
media/render-exploded.png
