BoujeeEnjinia1701/slopewatch/media/social-preview.png

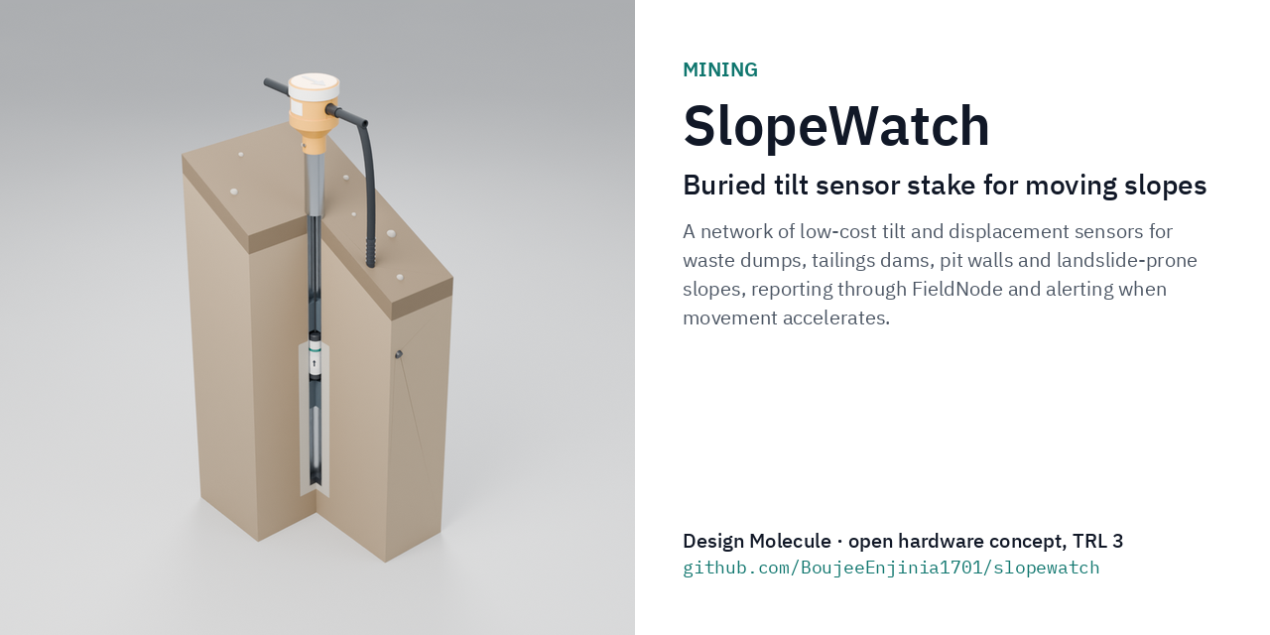
media/social-preview.png
